ew1abz/fc-510/Altera/Diags/timing.gif

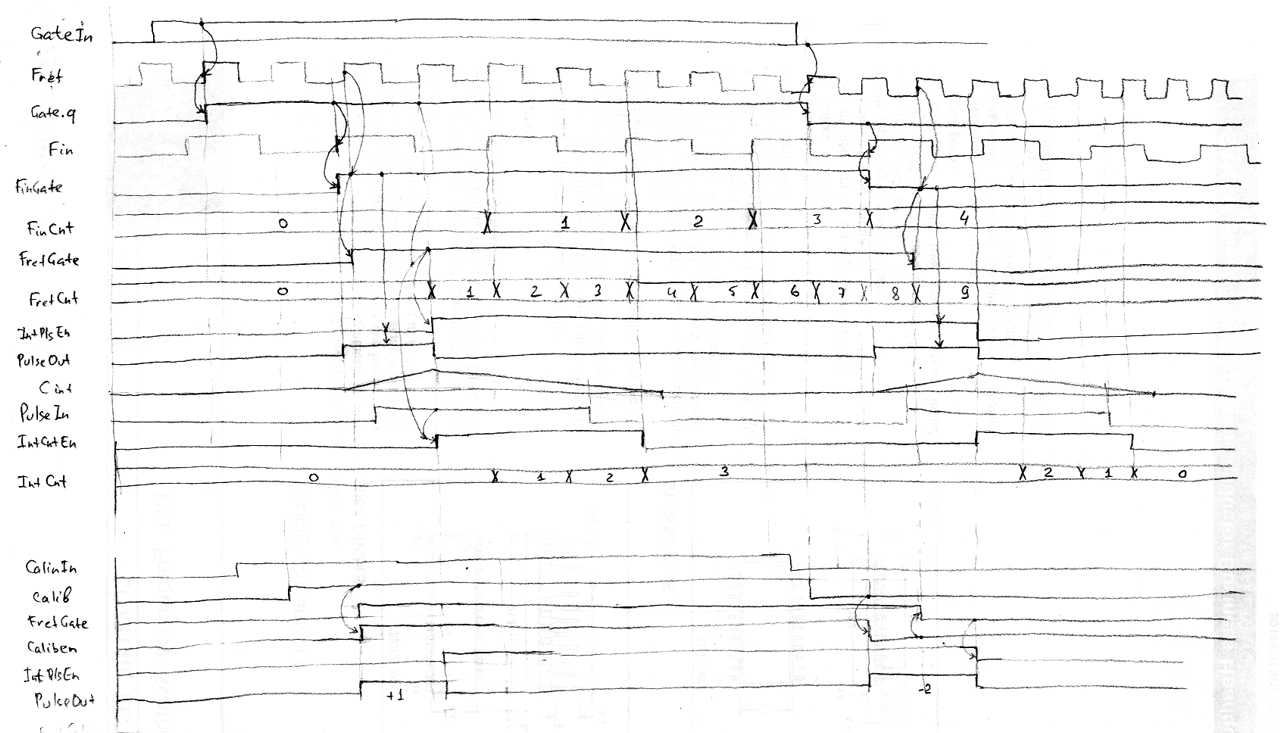
Altera/Diags/timing.gif
