ew1abz/fc-510/Photos1/FC-510_lcd_1602.jpg

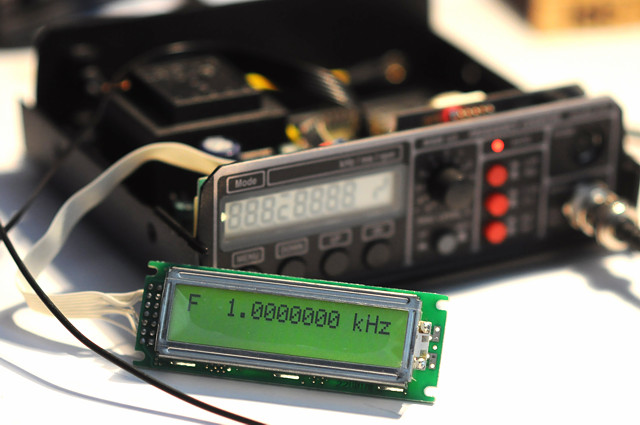
Photos1/FC-510_lcd_1602.jpg
