ew1abz/fc-510/Photos1/FC-510_prescaler_in.jpg

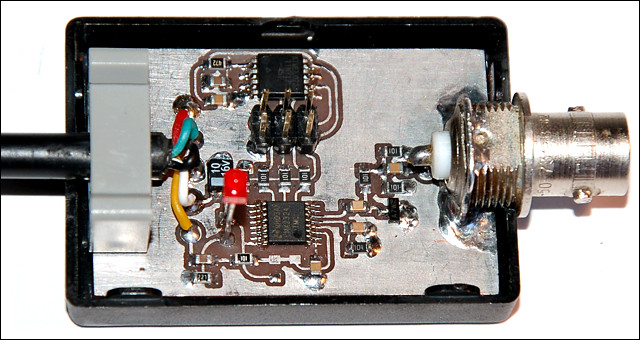
Photos1/FC-510_prescaler_in.jpg
