ew1abz/fc-510/Photos1/FC-510_terminal.gif

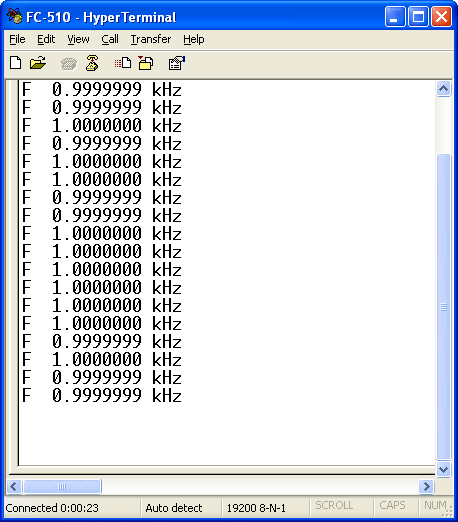
Photos1/FC-510_terminal.gif
