ew1abz/fc-510/Photos2/FC-510_front_board2.jpg

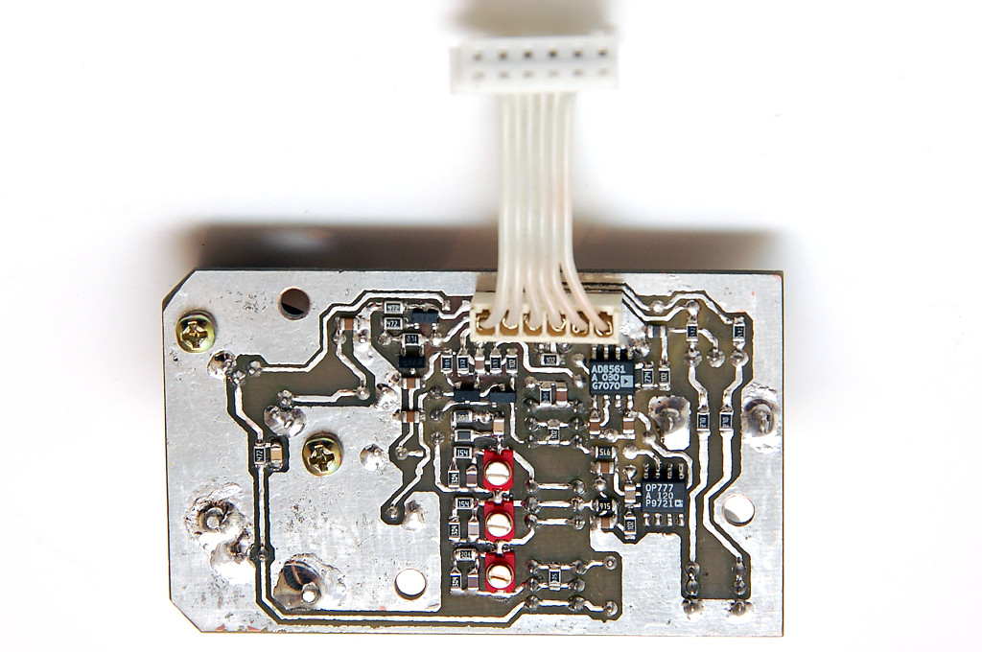
Photos2/FC-510_front_board2.jpg
