ew1abz/fc-510/Photos2/FC-510_front_panel2.jpg

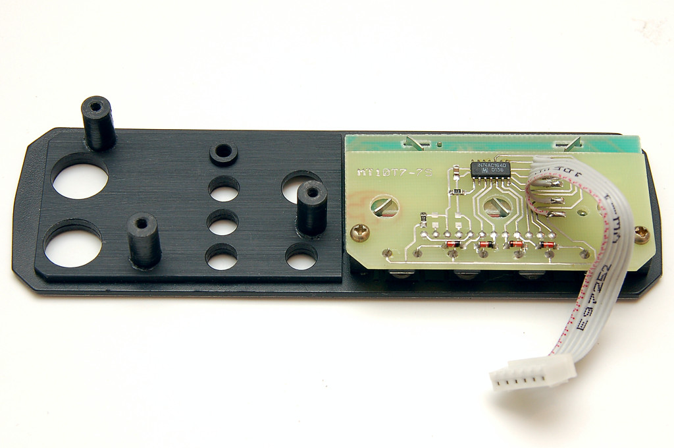
Photos2/FC-510_front_panel2.jpg
