ew1abz/fc-510/Photos2/FC-510_front_panel3.jpg

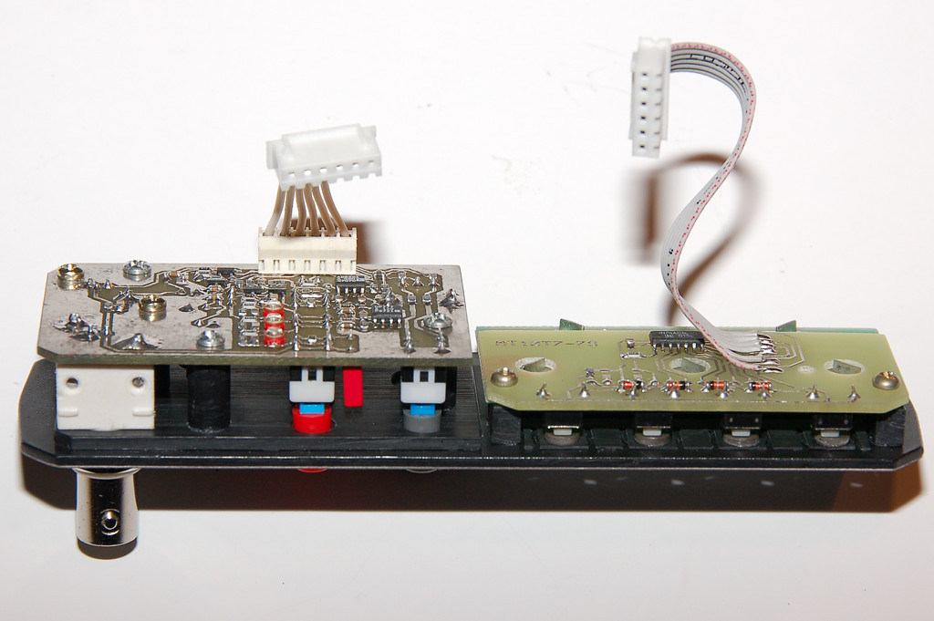
Photos2/FC-510_front_panel3.jpg
