ew1abz/fc-510/Photos2/FC-510_internals4.jpg

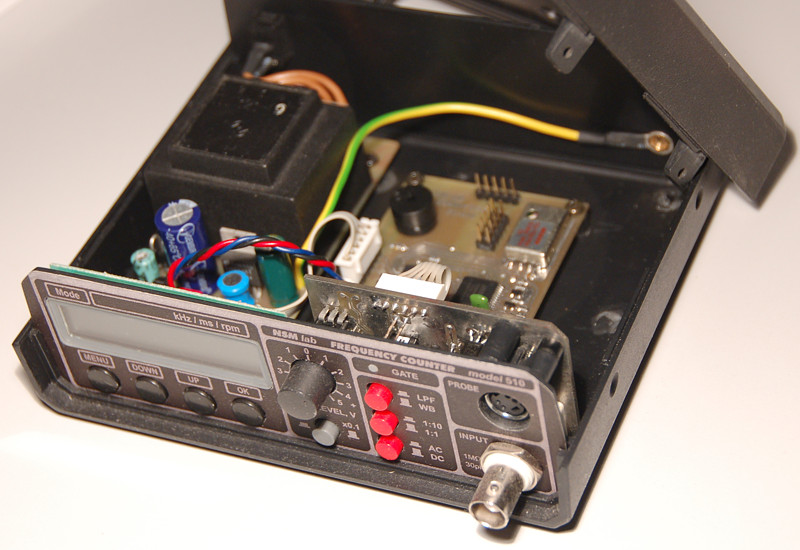
Photos2/FC-510_internals4.jpg
