ew1abz/fc-510/Photos2/FC-510_panel_front_det.jpg

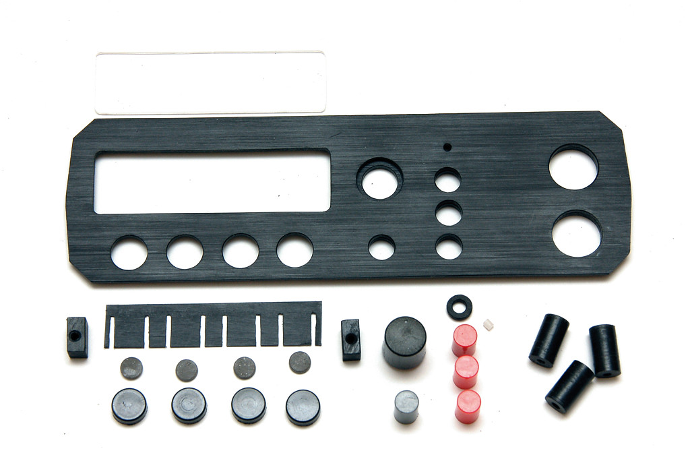
Photos2/FC-510_panel_front_det.jpg
