ew1abz/fc-510/Photos3/FC-510_panel_do_mech.jpg

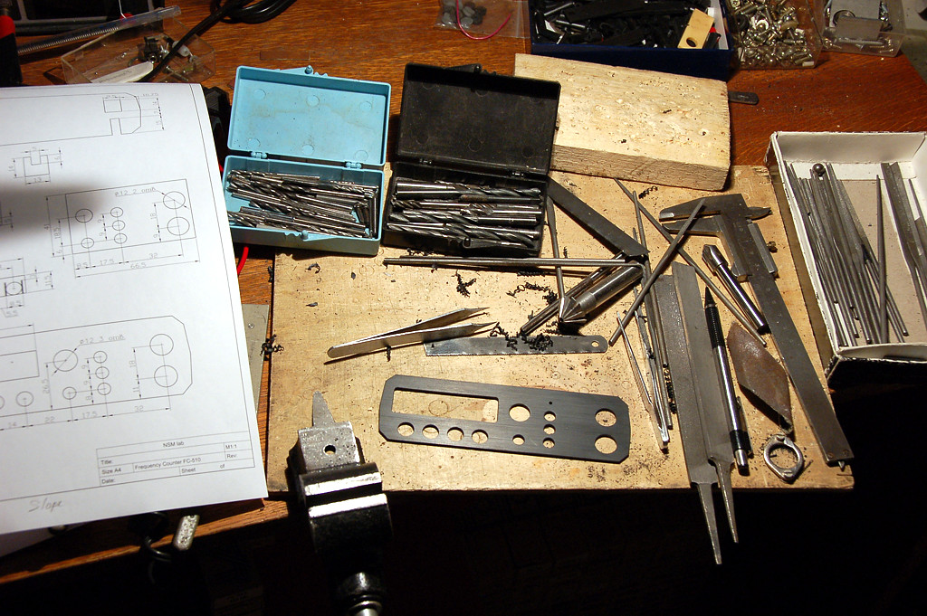
Photos3/FC-510_panel_do_mech.jpg
