ew1abz/fc-510/Pcad/Lut/pw-510_lut.pdf

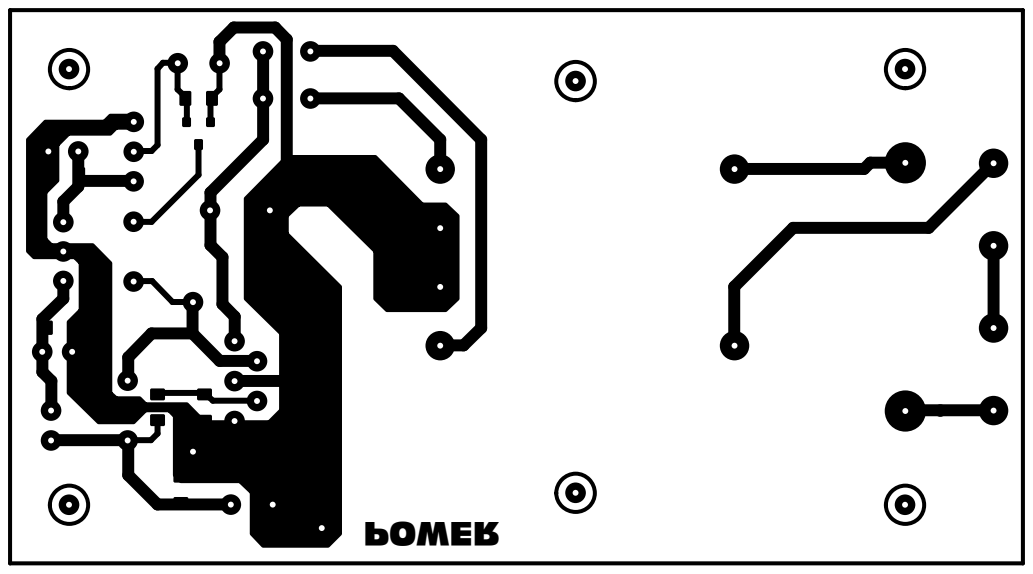
[picture p38: page 1]
POWER
