ew1abz/fc-510/Pcad/Lut/fc-510_lut.pdf

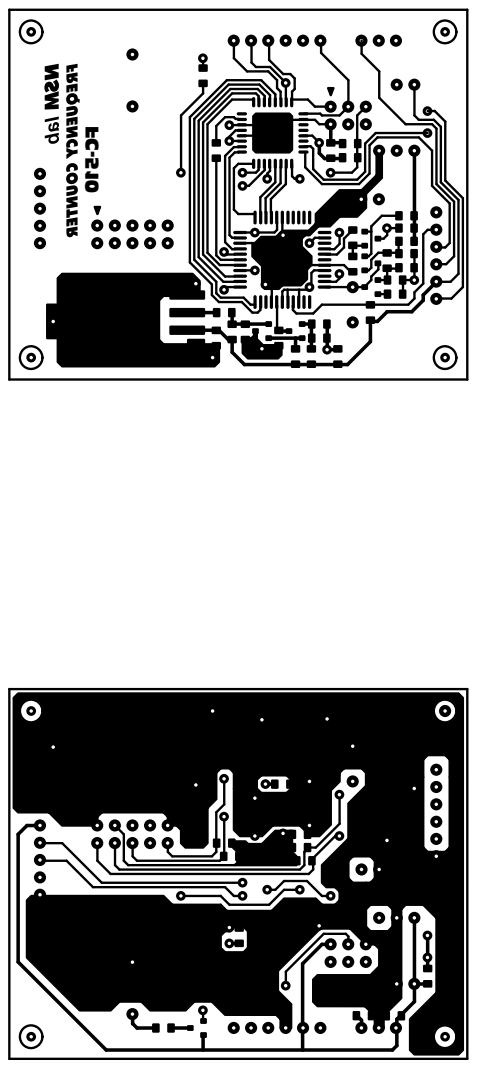
[picture p48: page 1]
