ew1abz/fc-510/Pcad/Lut/fp-510_lut.pdf

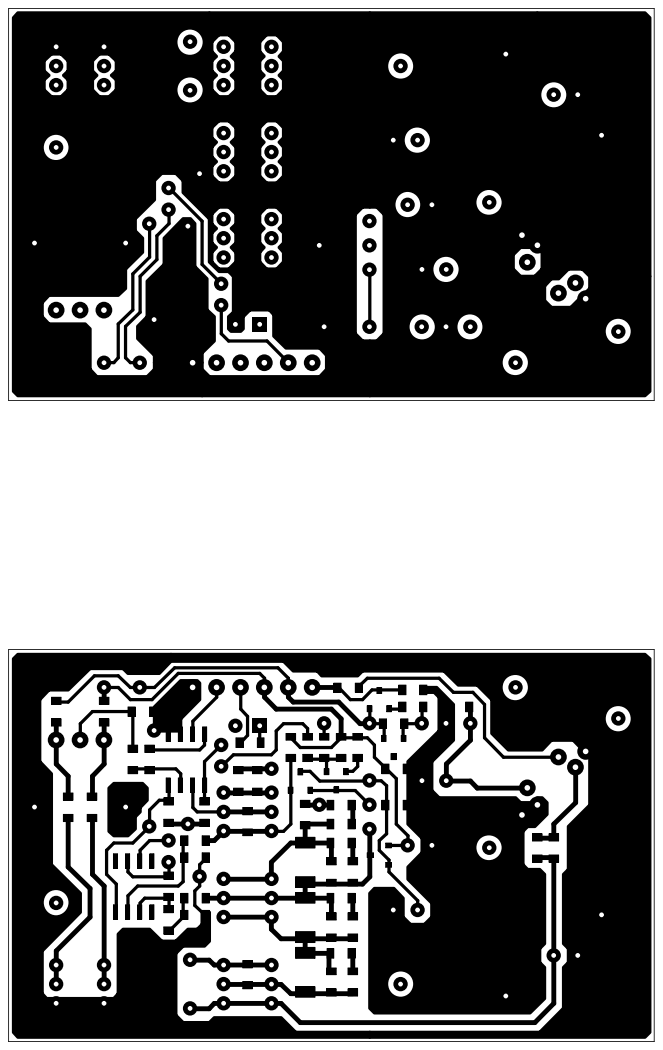
[picture p49: page 1]
