ew1abz/fc-510/Pcad/Lut/pl-510_lut.pdf

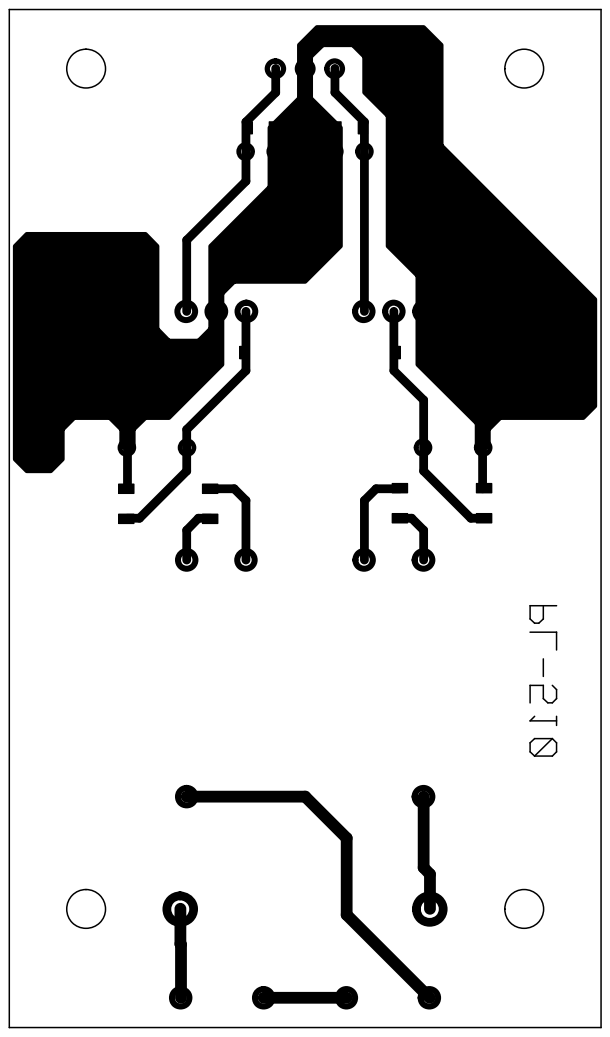
[picture p50: page 1]
