ew1abz/fc-510/Iar_C/Lcd.h

//----------------------------------------------------------------------------

//LCD support module: header file

//----------------------------------------------------------------------------

#ifndef LcdH
#define LcdH

//------------------------- Function prototypes: -----------------------------

void LCD_Init(void);     //LCD init
void LCD_Pos(char pos);  //set LCD position
void LCD_WrData(char d); //write data to LCD

//----------------------------------------------------------------------------

#endif
