ew1abz/fc-510/Iar_C/Menu.h

//----------------------------------------------------------------------------

//Frequency Counter FC-510
//Menu implementation module: header file

//----------------------------------------------------------------------------

#ifndef MenuH
#define MenuH

//------------------------- Function prototypes: -----------------------------

void Menu_Init(void);  //menu init
void Menu_Exe(bool t); //menu execute

//----------------------------------------------------------------------------

#endif
